kc9mne/PicoFox2/firmware/audio.h

/* PicoFox Audio Binary */

#define DEFAULT_AUDIO_LOOPS 6

// Heading for generated audio.
const uint8_t wavHeader[] {
  0x52, 0x49, 0x46, 0x46, 0x04, 0x94, 0x04, 0x00, 0x57, 0x41, 0x56, 0x45, 0x66, 0x6d, 0x74, 0x20, 0x10, 0x00, 0x00, 0x00, 0x01, 0x00,
  0x01, 0x00, 0x88, 0x13, 0x00, 0x00, 0x10, 0x27, 0x00, 0x00, 0x02, 0x00, 0x10, 0x00, 0x64, 0x61, 0x74, 0x61, 0xe0, 0x93, 0x04, 0x00
};

// Default audio wav (missing header).
const uint8_t defaultAudio[] {
  0xff, 0xff, 0x02, 0x00, 0xfd, 0xff, 0x03, 0x00, 0xfe, 0xff, 0x00, 0x00, 0x02, 0x00, 0xfc, 0xff, 0x05, 0x00, 0xfb, 0xff, 0x05, 0x00,
  0xfb, 0xff, 0x05, 0x00, 0xfc, 0xff, 0x04, 0x00, 0xfc, 0xff, 0x02, 0x00, 0x00, 0x00, 0x00, 0x00, 0x01, 0x00, 0xfe, 0xff, 0x01, 0x00,
  0x00, 0x00, 0x00, 0x00, 0x01, 0x00, 0xfe, 0xff, 0x01, 0x00, 0x00, 0x00, 0xff, 0xff, 0x02, 0x00, 0xfe, 0xff, 0x01, 0x00, 0xff, 0xff,
  0x01, 0x00, 0xff, 0xff, 0x01, 0x00, 0xff, 0xff, 0x01, 0x00, 0xff, 0xff, 0x01, 0x00, 0xff, 0xff, 0x01, 0x00, 0xff, 0xff, 0x01, 0x00,
  0xff, 0xff, 0x00, 0x00, 0x01, 0x00, 0xff, 0xff, 0x00, 0x00, 0x01, 0x00, 0xfe, 0xff, 0x02, 0x00, 0xff, 0xff, 0x00, 0x00, 0x00, 0x00,
  0x00, 0x00, 0x01, 0x00, 0xff, 0xff, 0x00, 0x00, 0x01, 0x00, 0xfe, 0xff, 0x03, 0x00, 0xfc, 0xff, 0x04, 0x00, 0xfd, 0xff, 0x02, 0x00,
  0xff, 0xff, 0xff, 0xff, 0x02, 0x00, 0xff, 0xff, 0xff, 0xff, 0x03, 0x00, 0xfc, 0xff, 0x03, 0x00, 0xff, 0xff, 0xff, 0xff, 0x03, 0x00,
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
  0xf5, 0xfe, 0x95, 0xed, 0xb8, 0xe0, 0x8b, 0xdb, 0x67, 0xdf, 0x5a, 0xeb, 0x71, 0xfc, 0x80, 0x0e, 0x01, 0x1d, 0x61, 0x24, 0xc5, 0x22,
  0x88, 0x18, 0x2d, 0x08, 0xc1, 0xf5, 0xc9, 0xe5, 0x48, 0xdc, 0x94, 0xdb, 0xea, 0xe3, 0x38, 0xf3, 0xc5, 0x05, 0xeb, 0x16, 0x7d, 0x22,
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
};
